RusikOk/-BluePill-to-J-Link-OB-v1.0/2_datasheet/MP2307.jpg

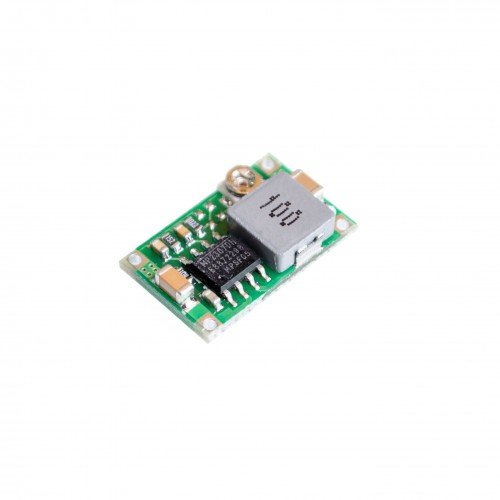
2_datasheet/MP2307.jpg
