RusikOk/-BluePill-to-J-Link-OB-v1.0/5_SolidWorks2020/untitled.47.png

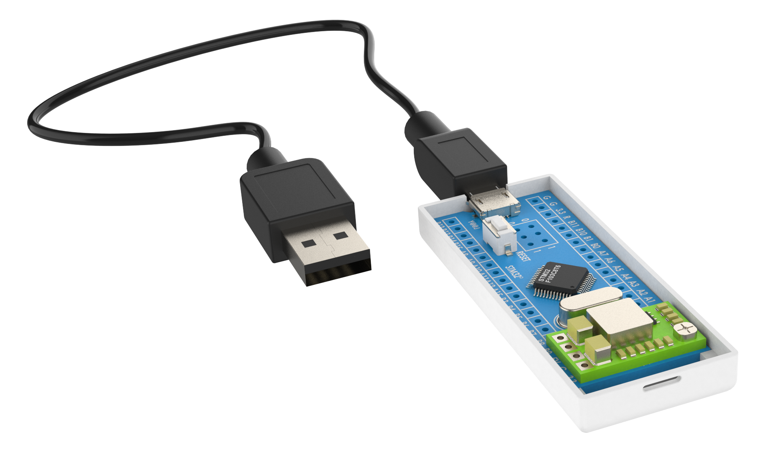
5_SolidWorks2020/untitled.47.png
