RusikOk/-BluePill-to-J-Link-OB-v1.0/7_photo/P10422-082825.jpg

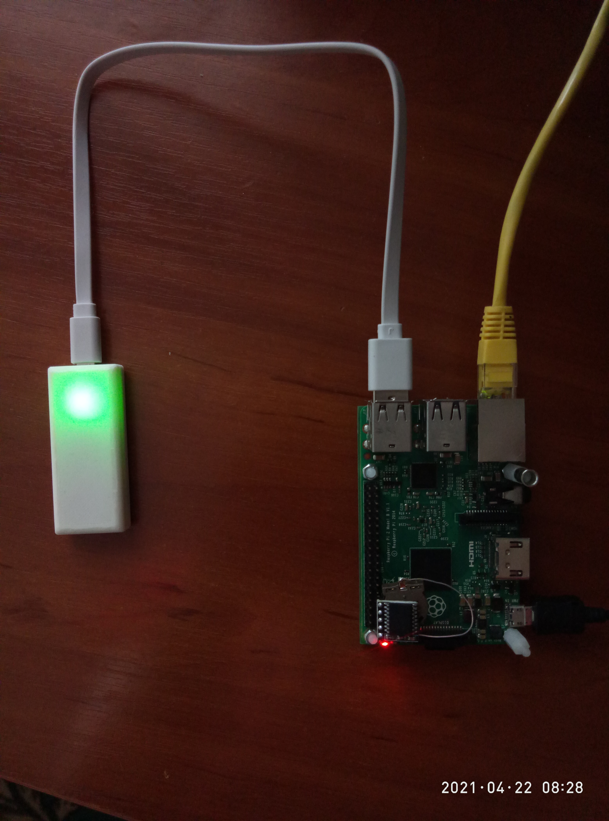
7_photo/P10422-082825.jpg
