RusikOk/-BluePill-to-J-Link-OB-v1.0/7_photo/P10424-124201.jpg

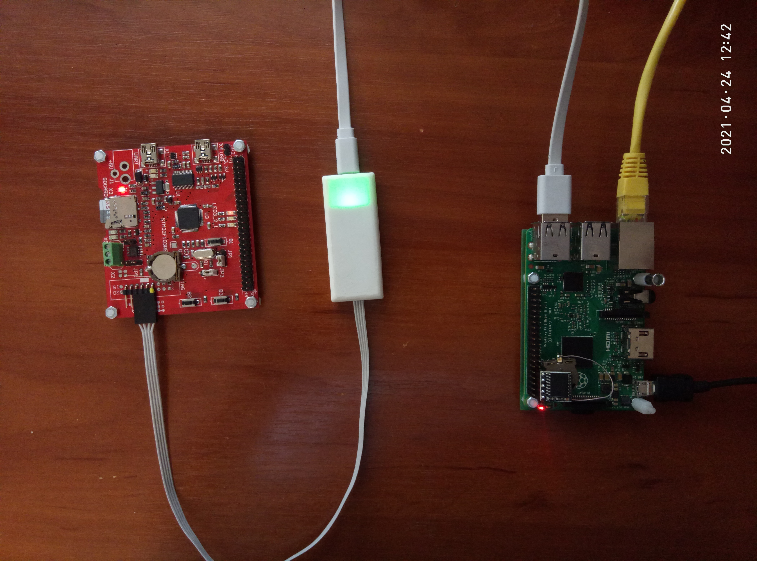
7_photo/P10424-124201.jpg
